ikesato/pic_analyze_remocon_pic18f2550/Firmware/HardwareProfile.h

/********************************************************************
 FileName:     	HardwareProfile - PICDEM FSUSB.h
 Dependencies:  See INCLUDES section
 Processor:     PIC18 USB Microcontrollers
 Hardware:      PICDEM FSUSB
 Compiler:      Microchip C18
 Company:       Microchip Technology, Inc.

 Software License Agreement:

 The software supplied herewith by Microchip Technology Incorporated
 (the �Company�) for its PIC� Microcontroller is intended and
 supplied to you, the Company�s customer, for use solely and
 exclusively on Microchip PIC Microcontroller products. The
 software is owned by the Company and/or its supplier, and is
 protected under applicable copyright laws. All rights are reserved.
 Any use in violation of the foregoing restrictions may subject the
 user to criminal sanctions under applicable laws, as well as to
 civil liability for the breach of the terms and conditions of this
 license.

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
********************************************************************
 File Description:

 Change History:
  Rev   Date         Description
  1.0   11/19/2004   Initial release
  2.1   02/26/2007   Updated for simplicity and to use common
                     coding style
  2.3   09/15/2008   Broke out each hardware platform into its own
                     "HardwareProfile - xxx.h" file
********************************************************************/

#ifndef HARDWARE_PROFILE_PICDEM_FSUSB_H
#define HARDWARE_PROFILE_PICDEM_FSUSB_H

    /*******************************************************************/
    /******** USB stack hardware selection options *********************/
    /*******************************************************************/
    //This section is the set of definitions required by the MCHPFSUSB
    //  framework.  These definitions tell the firmware what mode it is
    //  running in, and where it can find the results to some information
    //  that the stack needs.
    //These definitions are required by every application developed with
    //  this revision of the MCHPFSUSB framework.  Please review each
    //  option carefully and determine which options are desired/required
    //  for your application.

    //The PICDEM FS USB Demo Board platform supports the USE_SELF_POWER_SENSE_IO
    //and USE_USB_BUS_SENSE_IO features.  Uncomment the below line(s) if
    //it is desireable to use one or both of the features.
    //#define USE_SELF_POWER_SENSE_IO
    //#define tris_self_power     TRISAbits.TRISA2    // Input
    #if defined(USE_SELF_POWER_SENSE_IO)
    #define self_power          PORTAbits.RA2
    #else
    #define self_power          1
    #endif

    //#define USE_USB_BUS_SENSE_IO
    //#define tris_usb_bus_sense  TRISAbits.TRISA1    // Input
    #if defined(USE_USB_BUS_SENSE_IO)
    #define USB_BUS_SENSE       PORTAbits.RA1
    #else
    #define USB_BUS_SENSE       1
    #endif


    //Uncomment the following line to make the output HEX of this  
    //  project work with the MCHPUSB Bootloader    
    //#define PROGRAMMABLE_WITH_USB_MCHPUSB_BOOTLOADER
	
    //Uncomment the following line to make the output HEX of this 
    //  project work with the HID Bootloader
    #define PROGRAMMABLE_WITH_USB_HID_BOOTLOADER

    /*******************************************************************/
    /*******************************************************************/
    /*******************************************************************/
    /******** Application specific definitions *************************/
    /*******************************************************************/
    /*******************************************************************/
    /*******************************************************************/

    /** Board definition ***********************************************/
    //These defintions will tell the main() function which board is
    //  currently selected.  This will allow the application to add
    //  the correct configuration bits as wells use the correct
    //  initialization functions for the board.  These defitions are only
    //  required in the stack provided demos.  They are not required in
    //  final application design.
    #define DEMO_BOARD PICDEM_FS_USB
    #define PICDEM_FS_USB
    #define CLOCK_FREQ 48000000

    /** SWITCH *********************************************************/
    #define sw2                 PORTBbits.RB4
    
#endif  //HARDWARE_PROFILE_PICDEM_FSUSB_H
